AlexEsqu/G-Love/Code/includes/G_Love.h

#ifndef G_LOVE_H
#define G_LOVE_H

#include <stdint.h>
#include <iom328p.h>
#include <util/delay.h>
#include <avr/interrupt.h>

#include <config.h>
#include <uart.h>
#include <i2c.h>

#include <imu.h>
#include <touchscreen.h>
#include <adc.h>

void setup(void);

#endif
