AlexEsqu/G-Love/Code/srcs/touchscreen.c

#include <G_Love.h>

void touchscreen_read(touchscreen_data_t *data)
{
    uint8_t buf[6];
    i2c_read_burst(TOUCHSCREEN_ADDR, 0x01, buf, 6);
    if (buf[0] > 0) // Vérifie si un point de contact est détecté
    {
        data->x = ((buf[1] & 0x0F) << 8) | buf[2];
        data->y = ((buf[3] & 0x0F) << 8) | buf[4];
        data->gesture = buf[5];
    }
}
